mekatronik-achmadi/custom_ecu/images/aki.jpg

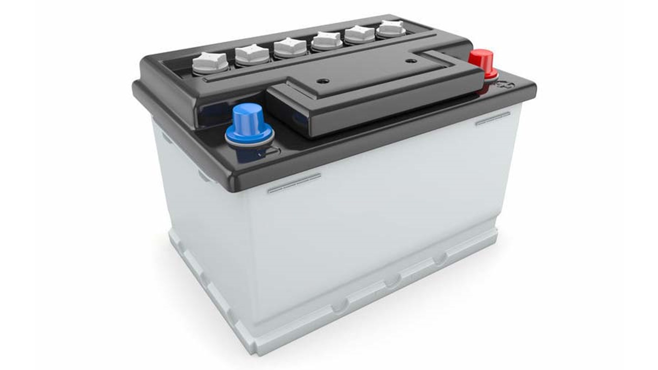
images/aki.jpg
