mekatronik-achmadi/custom_ecu/images/basic_f051r8.png

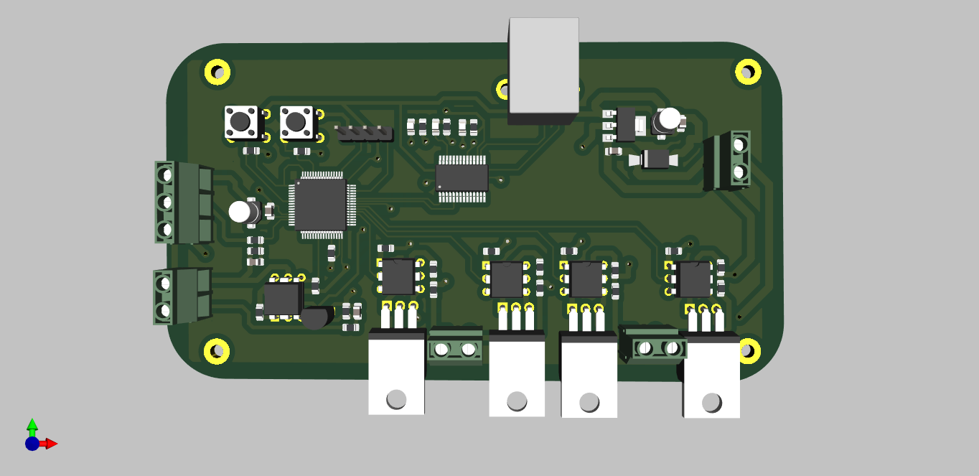
images/basic_f051r8.png
