mekatronik-achmadi/custom_ecu/images/laptop.png

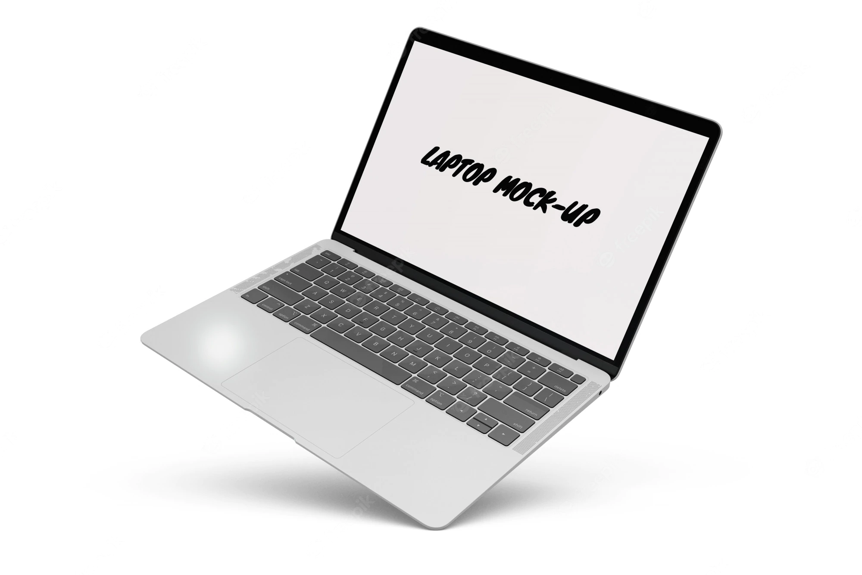
images/laptop.png
